wendlers/tinr2d2/src/pyremote/assets/robot_abwd_bbwd.png

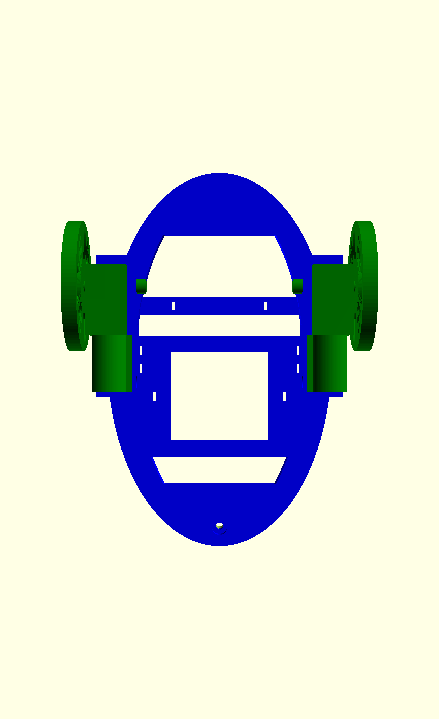
src/pyremote/assets/robot_abwd_bbwd.png
