wendlers/tinr2d2/cad/print/print_front_wheel_leg2.stl

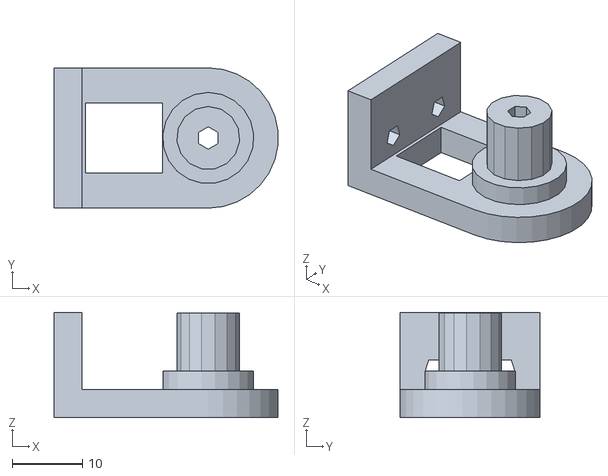
[picture p22: CAD file, 2014-01-27]
cad/print/print_front_wheel_leg2.stl
31.9 x 20.0 x 15.0
