wendlers/tinr2d2/cad/export/stl/wheel1.stl

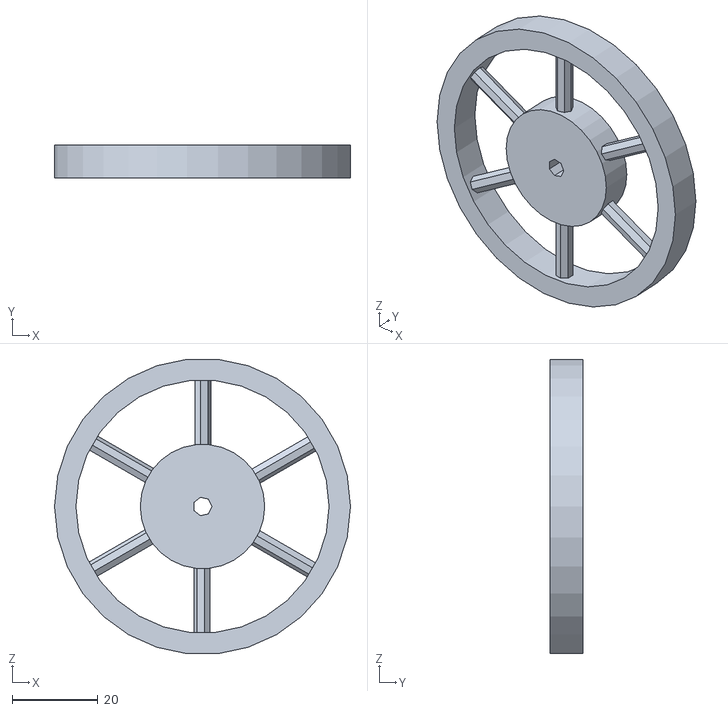
[picture p23: CAD file, 2014-01-13]
cad/export/stl/wheel1.stl
69.0 x 7.60 x 68.6
