wendlers/tinr2d2/cad/export/stl/dome_top.stl

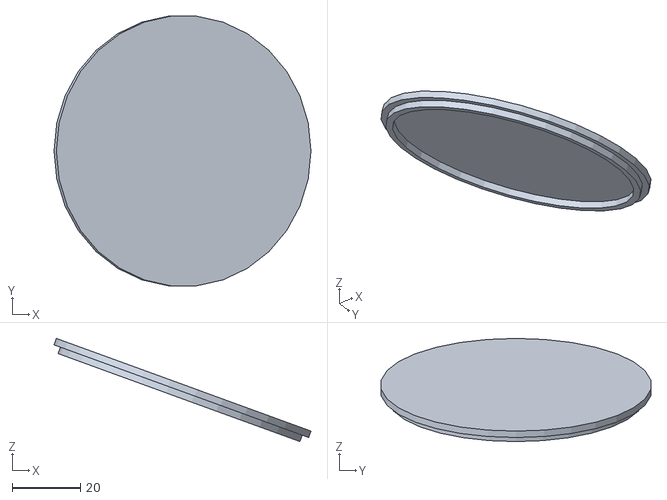
[picture p24: CAD file, 2014-01-13]
cad/export/stl/dome_top.stl
75.4 x 79.1 x 30.3
