wendlers/tinr2d2/cad/export/stl/motor1.stl

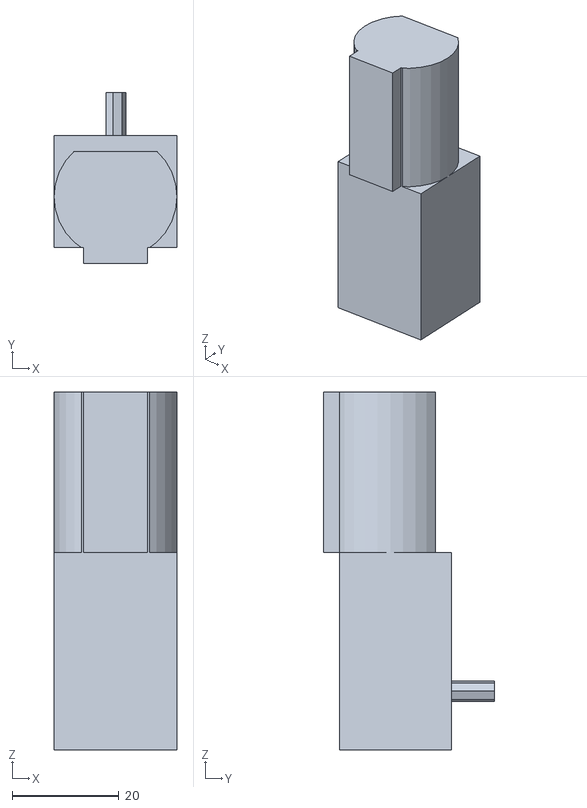
[picture p25: CAD file, 2014-01-13]
cad/export/stl/motor1.stl
23.0 x 32.0 x 67.0
