wendlers/tinr2d2/cad/print/print_front_wheel.stl

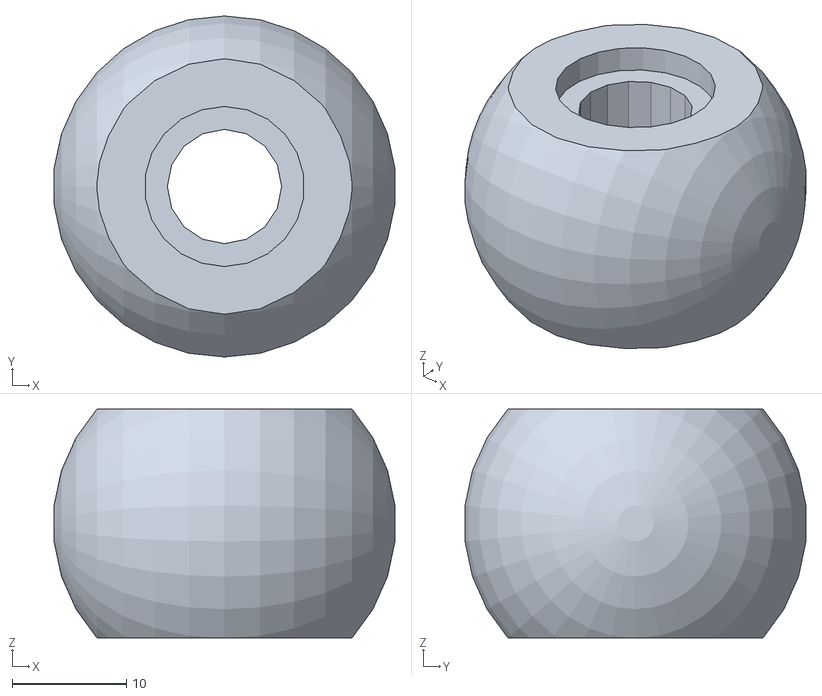
[picture p26: CAD file, 2014-01-13]
cad/print/print_front_wheel.stl
29.8 x 29.8 x 20.0
