wendlers/tinr2d2/cad/export/stl/top_base.stl

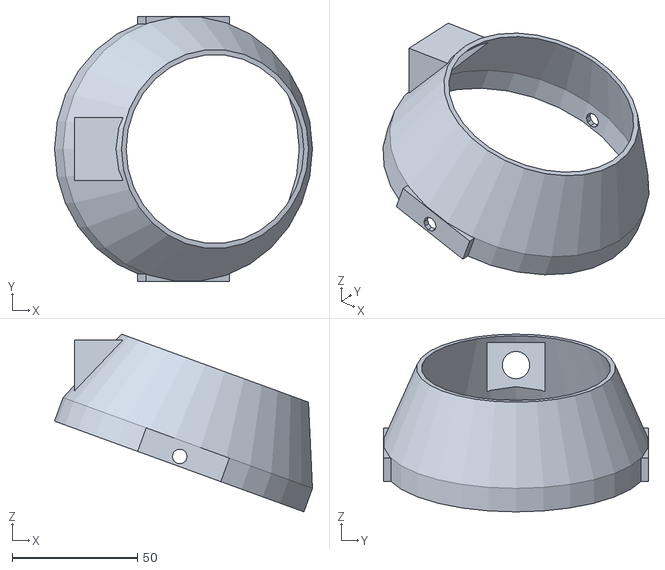
[picture p27: CAD file, 2014-01-13]
cad/export/stl/top_base.stl
103.0 x 106.0 x 71.0
